benmcevoy/pico-synth/src/synth/include/waveform.h

#ifndef SYNTH_WAVEFORM_
#define SYNTH_WAVEFORM_

#include "audiocontext.h"

#define WAVE_TABLE_LENGTH 512
#define FIX16_WAVE_TABLE_LENGTH 33554432

void synth_waveform_init();

// TODO: probably should be set_frequency on voice?
static inline void synth_waveform_set_wavetable_stride(voice_t* voice, fix16 pitch_bend) {
  voice->wavetable_stride =
      multfix16(divfix16(multfix16(voice->frequency, pitch_bend + voice->detune),
                         FIX16_SAMPLE_RATE),
                FIX16_WAVE_TABLE_LENGTH);
}

/*! \brief Generate an audio sample
 *
 * \param context The audio context
 */
fix16 synth_waveform_sample(voice_t* voice, fix16 pitch_bend);

fix16 synth_waveform_noise();

static fix16 sine_wave_table[WAVE_TABLE_LENGTH] = {
    0,      804,    1608,   2412,   3215,   4018,   4821,   5622,   6423,
    7223,   8022,   8819,   9616,   10410,  11204,  11995,  12785,  13573,
    14359,  15142,  15923,  16702,  17479,  18253,  19024,  19792,  20557,
    21319,  22078,  22833,  23586,  24334,  25079,  25820,  26557,  27291,
    28020,  28745,  29465,  30181,  30893,  31600,  32302,  32999,  33692,
    34379,  35061,  35738,  36409,  37075,  37736,  38390,  39039,  39682,
    40319,  40950,  41575,  42194,  42806,  43412,  44011,  44603,  45189,
    45768,  46340,  46906,  47464,  48015,  48558,  49095,  49624,  50146,
    50660,  51166,  51665,  52155,  52639,  53114,  53581,  54040,  54491,
    54933,  55368,  55794,  56212,  56621,  57022,  57414,  57797,  58172,
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
    19712,  19968,  20224,  20480,  20736,  20992,  21248,  21504,  21760,
    22016,  22272,  22528,  22784,  23040,  23296,  23552,  23808,  24064,
    24320,  24576,  24832,  25088,  25344,  25600,  25856,  26112,  26368,
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

#endif
