benmcevoy/pico-synth/src/synth/include/pitchtable.h

#ifndef SYNTH_PITCHTABLE_
#define SYNTH_PITCHTABLE_

#include <stdlib.h>

#include "fixedpoint.h"

// pitches as fix16 representations

#define PITCH_C0 2143223
#define PITCH_Db0 2270691
#define PITCH_D0 2405695
#define PITCH_Eb0 2548760
#define PITCH_E0 2700279
#define PITCH_F0 2860908
#define PITCH_Gb0 3030974
#define PITCH_G0 3211198

#define PITCH_Ab1 3402170
#define PITCH_A1 3604480
#define PITCH_Bb1 3818782
#define PITCH_B1 4045864
#define PITCH_C1 4286447
#define PITCH_Db1 4541382
#define PITCH_D1 4811390
#define PITCH_Eb1 5097521
#define PITCH_E1 5400625
#define PITCH_F1 5721751
#define PITCH_Gb1 6062014
#define PITCH_G1 6422462

#define PITCH_Ab2 6804340
#define PITCH_A2 7208960
#define PITCH_Bb2 7637630
#define PITCH_B2 8091795
#define PITCH_C2 8572960
#define PITCH_Db2 9082699
#define PITCH_D2 9622781
#define PITCH_Eb2 10194976
#define PITCH_E2 10801250
#define PITCH_F2 11443503
#define PITCH_Gb2 12123963
#define PITCH_G2 12844924

#define PITCH_Ab3 13608681
#define PITCH_A3 14417920
#define PITCH_Bb3 15275261
#define PITCH_B3 16183590
#define PITCH_C3 17145921
#define PITCH_Db3 18165465
#define PITCH_D3 19245629
#define PITCH_Eb3 20390019
#define PITCH_E3 21602500
#define PITCH_F3 22887006
#define PITCH_Gb3 24247926
#define PITCH_G3 25689784

#define PITCH_Ab4 27217428
#define PITCH_A4 28835840
#define PITCH_Bb4 30550523
#define PITCH_B4 32367116
#define PITCH_C4 34291777
#define PITCH_Db4 36330864
#define PITCH_D4 38491258
#define PITCH_Eb4 40780038
#define PITCH_E4 43204935
#define PITCH_F4 45774012
#define PITCH_Gb4 48495919
#define PITCH_G4 51379634

#define PITCH_Ab5 54434791
#define PITCH_A5 57671680
#define PITCH_Bb5 61101047
#define PITCH_B5 64734298
#define PITCH_C5 68583555
#define PITCH_Db5 72661794
#define PITCH_D5 76982452
#define PITCH_Eb5 81560076
#define PITCH_E5 86409871
#define PITCH_F5 91548090
#define PITCH_Gb5 96991838
#define PITCH_G5 102759268

#define PITCH_Ab6 108869648
#define PITCH_A6 115343360
#define PITCH_Bb6 122202030
#define PITCH_B6 129468530
#define PITCH_C6 137167175
#define PITCH_Db6 145323524
#define PITCH_D6 153964904
#define PITCH_Eb6 163120152
#define PITCH_E6 172819808
#define PITCH_F6 183096180
#define PITCH_Gb6 193983610
#define PITCH_G6 205518536

#define PITCH_Ab7 217739296
#define PITCH_A7 230686720
#define PITCH_Bb7 244404060
#define PITCH_B7 258937061
#define PITCH_C7 274334285
#define PITCH_Db7 290647048
#define PITCH_D7 307929808
#define PITCH_Eb7 326240305
#define PITCH_E7 345639616
#define PITCH_F7 366192361
#define PITCH_Gb7 387967221
#define PITCH_G7 411037073

#define PITCH_Ab8 435478593
#define PITCH_A8 461373440
#define PITCH_Bb8 488808120
#define PITCH_B8 517874122
#define PITCH_C8 548668571
#define PITCH_Db8 581294096
#define PITCH_D8 615859617
#define PITCH_Eb8 652480610
#define PITCH_E8 691279233
#define PITCH_F8 732384722
#define PITCH_Gb8 775934443
#define PITCH_G8 822074146

#endif
